ChrSchu90/PlatformIo.TCapChamp/src/Config.cpp

#define LOG_LEVEL NONE

#include "Config.h"
#include "SerialLogging.h"

/*
##############################################
##                  Config                  ##
##############################################
*/

Config::Config() : _preferences(new Preferences())
{
    _preferences->begin(KEY_SETTINGS_NAMESPACE, false);
    //_preferences->clear();

    temperatureConfig = new TemperatureConfig(_preferences);
    powerConfig = new PowerConfig(_preferences);
};

/*
##############################################
##            TemperatureConfig             ##
##############################################
*/

TemperatureConfig::TemperatureConfig(Preferences *preferences) : _preferences(preferences)
{
    // Check limit and round to 0.1
    _manualOutputActive = preferences->getBool(KEY_SETTING_TEMP_MANUAL_OUT_MODE, false);
    _manualOutputTemperature = preferences->getShort(KEY_SETTING_TEMP_MANUAL_OUT_TEMP, 150) / 10.0f;

    _manualInputActive = preferences->getBool(KEY_SETTING_TEMP_MANUAL_IN_MODE, false);
    _manualInputTemperature = preferences->getShort(KEY_SETTING_TEMP_MANUAL_IN_TEMP, 100) / 10.0f;

    for (size_t i = 0; i < TEMP_ADJUST_AMOUNT; i++)
    {
        _adjustments[i] = new TemperatureAdjustment(ADJUST_TEMP_START - i, preferences);
    }
};

bool TemperatureConfig::setManualOutputActive(bool manualMode)
{
    if (_manualOutputActive == manualMode)
    {
        return _manualOutputActive;
    }

    _manualOutputActive = manualMode;
    _preferences->putBool(KEY_SETTING_TEMP_MANUAL_OUT_MODE, _manualOutputActive);
    return _manualOutputActive;
}

bool TemperatureConfig::setManualInputActive(bool manualMode)
{
    if (_manualInputActive == manualMode)
    {
        return _manualInputActive;
    }

    _manualInputActive = manualMode;
    _preferences->putBool(KEY_SETTING_TEMP_MANUAL_IN_MODE, _manualInputActive);
    return _manualInputActive;
}

float TemperatureConfig::setManualOutputTemperature(float manualTemperature)
{
    // Check limit and round to 0.1
    manualTemperature = min(max(manualTemperature, (float)MIN_TEMPERATURE), (float)MAX_TEMPERATURE);
    manualTemperature = roundf(manualTemperature * 10) / 10;
    
    if (_manualOutputTemperature == manualTemperature)
    {
        return _manualOutputTemperature;
    }

    _manualOutputTemperature = manualTemperature;
    _preferences->putShort(KEY_SETTING_TEMP_MANUAL_OUT_TEMP, (int16_t)(_manualOutputTemperature * 10));
    return _manualOutputTemperature;
}

float TemperatureConfig::setManualInputTemperature(float manualTemperature)
{
    // Check limit and round to 0.1
    manualTemperature = min(max(manualTemperature, (float)MIN_TEMPERATURE), (float)MAX_TEMPERATURE);
    manualTemperature = roundf(manualTemperature * 10) / 10;

    if (_manualInputTemperature == manualTemperature)
    {
        return _manualInputTemperature;
    }

    _manualInputTemperature = manualTemperature;
    _preferences->putShort(KEY_SETTING_TEMP_MANUAL_IN_TEMP, (int16_t)(_manualInputTemperature * 10));
    return _manualInputTemperature;
}

float TemperatureConfig::getOutputTemperature(float inputTemp)
{
    if (_manualOutputActive)
    {
        return _manualOutputTemperature;
    }

    if (isnanf(inputTemp))
    {
        return inputTemp;
    }

    if(inputTemp > ADJUST_TEMP_START)
    {
        auto adj = _adjustments[0];
        return min(adj->getTemperatureAdjusted() - adj->tempReal + inputTemp, (float)MAX_TEMPERATURE);
    }

    if(inputTemp < ADJUST_TEMP_END)
    {
        auto adj = _adjustments[TEMP_ADJUST_AMOUNT - 1];
        return max(adj->getTemperatureAdjusted() - adj->tempReal + inputTemp, (float)MIN_TEMPERATURE);
    }

    int8_t upperIn = ceil(inputTemp); 
    int8_t lowerIn = floor(inputTemp);
    if(upperIn == lowerIn)
    {
        auto adj = getTempAdjustment(upperIn);
        if(adj != nullptr)
        {
            return adj->getTemperatureAdjusted();
        }
    }

    auto adjUpper = getTempAdjustment(upperIn);
    auto adjLower = getTempAdjustment(lowerIn);
    if(adjUpper != nullptr && adjLower != nullptr)
    {
        auto upperOut = adjUpper->getTemperatureAdjusted();
        auto lowerOut = adjLower->getTemperatureAdjusted();

        // Linear interpolation
        return lowerOut + (upperOut - lowerOut) / (upperIn - lowerIn) * (inputTemp - lowerIn);
    }

    return inputTemp;
}

TemperatureAdjustment *TemperatureConfig::getTempAdjustment(int8_t tempReal)
{
    for (size_t i = 0; i < TEMP_ADJUST_AMOUNT; i++)
    {
        auto adjustment = getAdjustment(i);
        if(adjustment->tempReal == tempReal)
        {
            return adjustment;
        }
    }

    return nullptr;
}

/*
##############################################
##          TemperatureAdjustment           ##
##############################################
*/

TemperatureAdjustment::TemperatureAdjustment(int8_t tempReal, Preferences *preferences) : _preferences(preferences), tempReal(tempReal)
{
    auto keyOffset = String(KEY_SETTING_TEMP_ADJUST_TEMP_OFFSET) + tempReal;
    _tempOffset =  preferences->getChar(keyOffset.c_str(), 0) / 10.0f;
}

float TemperatureAdjustment::setTemperatureOffset(float offset)
{
    // Check limit and round to 0.1
    offset = min(max(offset, (float)(ADJUST_TEMP_MAX_OFSET * -1)), (float)(ADJUST_TEMP_MAX_OFSET));
    offset = roundf(offset * 10) / 10;

    if(offset == _tempOffset)
    {
        return _tempOffset;
    }

    _tempOffset = offset;
    auto keyOffset = String(KEY_SETTING_TEMP_ADJUST_TEMP_OFFSET) + tempReal;
    _preferences->putChar(keyOffset.c_str(), (int8_t)(_tempOffset * 10));
    return _tempOffset;
}

/*
##############################################
##            PowerConfig                   ##
##############################################
*/

PowerConfig::PowerConfig(Preferences *preferences) : _preferences(preferences)
{
    _manualOutputActive = preferences->getBool(KEY_SETTING_POWER_MANUAL_MODE, false);
    _manualPower = preferences->getUChar(KEY_SETTING_POWER_MANUAL_POWER, 100);

    for (size_t i = 0; i < POWER_AREA_AMOUNT; i++)
    {
        _areas[i] = new PowerArea(i, this, preferences);
    }
};

bool PowerConfig::setManualOutputActive(bool manualMode)
{
    if (_manualOutputActive == manualMode)
    {
        return _manualOutputActive;
    }

    _manualOutputActive = manualMode;
    _preferences->putBool(KEY_SETTING_POWER_MANUAL_MODE, _manualOutputActive);
    return _manualOutputActive;
}

uint8_t PowerConfig::setManualPower(uint8_t manualPower)
{
    // Check limit and round to next 5
    manualPower = min(max(manualPower, (uint8_t)MIN_POWER_LIMIT), (uint8_t)MAX_POWER_LIMIT);
    manualPower = ((uint8_t)round((manualPower + (uint8_t)(STEP_POWER_LIMIT / 2)) / STEP_POWER_LIMIT)) * STEP_POWER_LIMIT;

    if (_manualPower == manualPower)
    {
        return _manualPower;
    }

    _manualPower = manualPower;
    _preferences->putUChar(KEY_SETTING_POWER_MANUAL_POWER, _manualPower);
    return _manualPower;
}

uint8_t PowerConfig::getOutputPowerLimit(float inputTemp)
{
    if (_manualOutputActive)
    {
        return _manualPower;
    }

    if (isnanf(inputTemp))
    {
        return MIN_POWER_LIMIT;
    }

    auto area = getArea(inputTemp);
    if (area != nullptr)
    {
        return area->getPowerLimit();
    }

    return MIN_POWER_LIMIT;
}

PowerArea *PowerConfig::getArea(float temperature)
{
    if (isnanf(temperature))
    {
        return nullptr;
    }

    for (size_t i = 0; i < POWER_AREA_AMOUNT; i++)
    {
        auto area = getArea(i);
        if (area->isResponsable(temperature))
        {
            return area;
        }
    }

    return nullptr;
}

/*
##############################################
##             PowerArea                    ##
##############################################
*/

PowerArea::PowerArea(size_t index, PowerConfig *config, Preferences *preferences) : index(index), _config(config), _preferences(preferences)
{
    auto keyStart = String(KEY_SETTING_POWER_AREA_START) + index;
    _start = preferences->getShort(keyStart.c_str(), 0) / 10.0f;

    auto keyEnd = String(KEY_SETTING_POWER_AREA_END) + index;
    _end = preferences->getShort(keyEnd.c_str(), 0) / 10.0f;

    auto keyLimit = String(KEY_SETTING_POWER_AREA_LIMIT) + index;
    _powerLimit = preferences->getUChar(keyLimit.c_str(), MAX_POWER_LIMIT);
};

float PowerArea::setStart(float start)
{
    // Check limit and round to 0.1
    start = min(max(start, (float)MIN_TEMPERATURE), (float)MAX_TEMPERATURE);
    start = roundf(start * 10) / 10;

    if (start == _start)
    {
        return _start;
    }

    _start = start;
    auto keyStart = String(KEY_SETTING_POWER_AREA_START) + index;
    _preferences->putShort(keyStart.c_str(), (int16_t)(_start * 10));
    return _start;
}

float PowerArea::setEnd(float end)
{
    // Check limit and round to 0.1
    end = min(max(end, (float)MIN_TEMPERATURE), (float)MAX_TEMPERATURE);
    end = roundf(end * 10) / 10;

    if (end == _end)
    {
        return _end;
    }

    _end = end;
    auto keyEnd = String(KEY_SETTING_POWER_AREA_END) + index;
    _preferences->putShort(keyEnd.c_str(), (int16_t)(_end * 10));
    return _end;
}

uint8_t PowerArea::setPowerLimit(uint8_t powerLimit)
{
    // Check limit and round to next 5
    powerLimit = min(max(powerLimit, (uint8_t)MIN_POWER_LIMIT), (uint8_t)MAX_POWER_LIMIT);
    powerLimit = ((uint8_t)round((powerLimit + (uint8_t)(STEP_POWER_LIMIT / 2)) / STEP_POWER_LIMIT)) * STEP_POWER_LIMIT;
    if (powerLimit == _powerLimit)
    {
        return _powerLimit;
    }

    _powerLimit = powerLimit;
    auto keyLimit = String(KEY_SETTING_POWER_AREA_LIMIT) + index;
    _preferences->putUChar(keyLimit.c_str(), _powerLimit);
    return _powerLimit;
}

bool PowerArea::isResponsable(float temperature)
{
    return !isnanf(temperature) && isEnabled() && isValid() && temperature >= _start && temperature <= _end;
}

bool PowerArea::isValid()
{
    return _start <= _end && _end >= _start;
}
