ChrSchu90/PlatformIo.TCapChamp/include/Webinterface.h

#pragma once

#include "Config.h"

#define STYLE_HIDDEN "background-color: unset; width: 0px; height: 0px; display: none;"
#define STYLE_NUM_TEMP_ADJUST_NORMAL "width: 16%; color: black; background: rgba(255,255,255,0.8);"
#define STYLE_NUM_POWER_ADJUST_NORMAL "width: 16%; color: black; background: rgba(255,255,255,0.8);"
#define STYLE_NUM_POWER_ADJUST_ERROR "width: 16%; color: black; background: rgba(231,76,60,0.8);"
#define STYLE_NUM_POWER_ADJUST_DISABLED "width: 16%; color: black; background: rgba(153,153,153,0.8);"
#define STYLE_LBL_ADJUST "background-color: unset; width: 84%; text-align-last: left;"
#define STYLE_LBL_INOUT "width: 16%;"
#define STYLE_LBL_API "width: 29%;"
#define STYLE_SWITCH_INOUT "margin-bottom: 3px; width: 12.5%; vertical-align: middle; "
#define STYLE_NUM_INOUT_MANUAL_INPUT "width: 16%; color: black; background: rgba(255,255,255,0.8);"
#define STYLE_LBL_API_VALUE_OUTPUT "background-color: unset; text-align: left; width: 70.5%;"
#define STYLE_LBL_INOUT_VALUE_OUTPUT "background-color: unset; text-align: left; width: 83.5%;"
#define STYLE_LBL_INOUT_MANUAL_ENABLE "background-color: unset; text-align: left; width: 70%; vertical-align: bottom;" 


/// @brief Holds a available WiFi option
struct WiFiOption 
{
    String Label = emptyString;
    String Value = emptyString;
    uint16_t Control = 0;
};

/// @brief Implements a system information tab inside the Webinterface
class SystemInfoTab
{
private:
    static const int8_t REBOOT_CLICK_CNT = 5;
    static const int16_t AmountWiFiOptions = 10;
    int8_t _rebootCnt = REBOOT_CLICK_CNT;
    int8_t _credentialUpdateCnt = 0;
    uint16_t _tab;
    uint16_t _btnReboot;
    uint16_t _lblPerformance;
    uint16_t _lblInfoTest;
    uint16_t _selSsid;
    uint16_t _txtSsid;
    uint16_t _txtPassword;
    uint16_t _btnSave;
    uint16_t _btnScan;
    WiFiOption _wifiOptions[AmountWiFiOptions];

    void updateBtnSaveState();
    void wifiScanCompleted(int16_t networkCnt);

protected:
public:
    /// @brief Creates an instance of the SystemInfoTab
    SystemInfoTab();

    /// @brief Update the system information. NOTE: this function is called cyclically if a client is connected!
    void update();
};

/// @brief Web UI temperature element that represents a power limit area
class PowerAreaTab
{
private:
    PowerArea *_config;
    uint16_t _numStart;
    uint16_t _numEnd;
    uint16_t _numLimit;

protected:
public:
    /// @brief Creates a area for the power limit configuration inside the Web interface
    /// @param groupCtlId the parent control group ID
    /// @param config the power limit area configuration
    PowerAreaTab(const uint16_t groupCtlId, PowerArea *config);

    /// @brief Forces an update of the UI values
    void update();

    /// @brief Foreces an update of the status indicator to make a invalid configuration visible
    void updateStatus();
};

/// @brief Adjustements tab to define the manipulation of output temperature and power limit
class AdjustmentTab 
{
private:
    Config *_config;
    uint16_t _tab;

protected:
public:
    /// @brief Creates the adjustment tab instance
    /// @param config the configuration
    /// @param wifiManager the WiFi manager
    AdjustmentTab(Config *config);
};

/// @brief Web UI
class Webinterface
{
private:
    Config *_config;
    uint16_t _lblSensorTemp;
    uint16_t _lblWeatherTemp;
    uint16_t _swManualTempInput;
    uint16_t _swManualTempOutput;
    uint16_t _swManualPowerOutput;
    uint16_t _numManualTempInput;
    uint16_t _numManualTempOutput;
    uint16_t _numManualPowerOutput;
    uint16_t _lblTempOutput;
    uint16_t _lblTempTarget;
    uint16_t _lblPowerOutput;
    AdjustmentTab *_adjustmentTab;
    SystemInfoTab *_systemInfoTab;

protected:
public:

    /// @brief Creates the web UI instance
    /// @param port the webinterface port
    /// @param config the configuration
    /// @param wifiManager the WiFi manager
    Webinterface(const uint16_t port, Config *config);

    /// @brief Gets if any client is connected 
    bool getClientIsConnected();

    /// @brief Update the System and WiFi information inside the Webinterface-Tab if a client is connected
    void updateSystemInformation() { if(getClientIsConnected()) _systemInfoTab->update(); };

    /// @brief Updates the sensor temperature inside webinterface
    /// @param temperature the new temperature
    void setSensorTemp(const float temperature);

    /// @brief Updates the weather API temperature inside webinterface
    /// @param temperature the new temperature
    void setWeatherTemp(const float temperature, const String timestamp);

    /// @brief Updates the output temperature inside webinterface
    /// @param temperature the new output temperature
    void setOutputTemp(const float temperature);

    /// @brief Updates the target temperature inside webinterface
    /// @param temperature the new target temperature
    void setTargetTemp(const float temperature);

    /// @brief Updates the output power limit inside webinterface
    /// @param powerLimit the new power limit [%]
    void setOuputPowerLimit(const float powerLimit);
};
