ChrSchu90/PlatformIo.TCapChamp/include/Secrets.template.h

#pragma once

/// @brief API key for OpenWeatherMap. Can be created for free at
/// https://home.openweathermap.org/users/sign_up (60 calls/minute or 1,000,000 calls/month)
#define WEATHER_API_KEY ""

/// @brief City ID for weather API. Can be taken from https://openweathermap.org/ by search from URL (https://openweathermap.org/city/xxxxxxx)
#define WEATHER_CITY_ID 0

/// @brief City ID is sometimes very hard to find, instead you can use Latitude + Longitude (can be taken from google maps with right-click)
#define WEATHER_LATITUDE 0

/// @brief City ID is sometimes very hard to find, instead you can use Latitude + Longitude (can be taken from google maps with right-click)
#define WEATHER_LONGITUDE 0

/// @brief Initial password for WiFi configuration AP 
#define WIFI_CONFIG_PASSWORD "MyPassword"
